jnsltk/kiwave-sonar-system/SonarController/KiwiMQTT.h

#ifndef KiwiMQTT_h
#define KiwiMQTT_h
#include "Arduino.h"
#include "PubSubClient.h"
#include "rpcWiFi.h"
class KiwiMQTT {
    public:
    KiwiMQTT(char* ssid,char* secret);
    void init(); //Connects to chosen MQTT broker .
    void setServer(char* broker,int port); //Connects to chosen MQTT broker.
    void setCallback(void (*callback)(char*, uint8_t*, unsigned int));
    void publish(uint8_t* data,int dataLength);
    void publish(String data);
    bool sweep();
    void connect();
    bool getBrokerStatus();
    int getWiFiStatus();
    private:
    PubSubClient _pubSubClient;
    WiFiClient _wifiClient;
    char* _ssid;
    char* _secret;
    String _name;

};

#endif
